nowtechnologies/open_PAPR/blower/firmware/attiny85/main.cpp

/*
 * papr_blower_attiny85.cpp
 *
 * Author : vmp
 */ 

#include <stdint.h>
#include <avr/io.h>
#include "../application/applicationInterface.h"

int main(void) {
  applicationSetup();
  applicationLoop();
  while (1) {
  }
}
