nowtechnologies/open_PAPR/blower/firmware/stm32g031j6/papr_blower_stm32g031j6_bsp.cpp

/// STM32G031J6 Board Support Package

#include "main.h"
#include "bspInterface.h"
#include "applicationInterface.h"

extern ADC_HandleTypeDef hadc1;
extern DMA_HandleTypeDef hdma_adc1;
extern TIM_HandleTypeDef htim17;

namespace {
  constexpr uint32_t cAdcChannelCount = ((uint32_t)  4);
  constexpr uint32_t cAdcSampleCount = ((uint32_t)  64);
  constexpr uint32_t cAdcBufferSize =   ((uint32_t)  cAdcSampleCount * cAdcChannelCount);
  constexpr uint32_t cIndexAdcBattery =  0u;
  constexpr uint32_t cIndexAdcPotmeter = 1u;
  constexpr uint32_t cIndexAdcTemp =     2u;
  constexpr uint32_t cIndexAdcVref =     3u;
  
  volatile uint16_t adcBuffer[cAdcBufferSize];
  volatile uint32_t adcData[cAdcChannelCount];
  
  ADC_HandleTypeDef &handleAdc = hadc1;
  DMA_HandleTypeDef &handleDmaAdc = hdma_adc1;
  TIM_HandleTypeDef &handleTimer = htim17;
  uint32_t timerChannel = TIM_CHANNEL_1;
  
  /// Calculating ADC oversample average
  void calculateAndCopyAdcData(uint32_t const start, uint32_t const end) {
    for (unsigned int i = start; i < end; i++) {
      adcData[i % cAdcChannelCount] += adcBuffer[i];
      adcData[i % cAdcChannelCount] /= 2;
    }
  }
  
}

/// HAL callback
extern "C" void HAL_ADC_ConvCpltCallback(ADC_HandleTypeDef* hadc) {
  calculateAndCopyAdcData(cAdcBufferSize / 2, cAdcBufferSize);
}

/// HAL callback
extern "C" void HAL_ADC_ConvHalfCpltCallback(ADC_HandleTypeDef* hadc) {
  calculateAndCopyAdcData(0, cAdcBufferSize / 2);
}

extern "C" void applicationSetup() {
  // Calibrate ADC
  if (HAL_ADCEx_Calibration_Start(&handleAdc) != HAL_OK) {
    Error_Handler();
  }
  // Start ADC DMA
  if (HAL_ADC_Start_DMA(&handleAdc, (uint32_t *)adcBuffer, cAdcBufferSize) != HAL_OK) {
    Error_Handler();
  }
  // PWM Timer setup
  __HAL_TIM_SET_PRESCALER(&handleTimer, 3); //0 = 5.8 kHz, 1 = 2 kHz, 3 = 1.5 kHz (48 MHz CPU & 0xFFF max)
  HAL_TIM_PWM_Start(&handleTimer, timerChannel);
}

// System
uint32_t papr::getTick() {
  return HAL_GetTick();
}

void papr::delayMs(uint32_t const aDelayMs) {
  HAL_Delay(aDelayMs);
}

// Power LED
void papr::turnOnPowerLed() {
  //HAL_GPIO_WritePin(POWER_LED_GPIO_Port, POWER_LED_Pin, GPIO_PIN_SET);
}

void papr::turnOffPowerLed() {
  //HAL_GPIO_WritePin(POWER_LED_GPIO_Port, POWER_LED_Pin, GPIO_PIN_RESET);
}

void papr::togglePowerLed() {
  //HAL_GPIO_TogglePin(POWER_LED_GPIO_Port, POWER_LED_Pin);
}

bool papr::isPowerLedOn() {
  //return HAL_GPIO_ReadPin(POWER_LED_GPIO_Port, POWER_LED_Pin) == GPIO_PIN_SET;
  return false;
}

// Mode LED
void papr::turnOnModeLed() {
  HAL_GPIO_WritePin(MODE_LED_GPIO_Port, MODE_LED_Pin, GPIO_PIN_SET);
}

void papr::turnOffModeLed() {
  HAL_GPIO_WritePin(MODE_LED_GPIO_Port, MODE_LED_Pin, GPIO_PIN_RESET);
}

void papr::toggleModeLed() {
  HAL_GPIO_TogglePin(MODE_LED_GPIO_Port, MODE_LED_Pin);
}

bool papr::isModeLedOn() {
  return HAL_GPIO_ReadPin(MODE_LED_GPIO_Port, MODE_LED_Pin) == GPIO_PIN_SET;
}

// Buzzer
void papr::turnOnBuzzer() {
  HAL_GPIO_WritePin(BUZZER_GPIO_Port, BUZZER_Pin, GPIO_PIN_SET);
}

void papr::turnOffBuzzer() {
  HAL_GPIO_WritePin(BUZZER_GPIO_Port, BUZZER_Pin, GPIO_PIN_RESET);
}

bool papr::isBuzzerOn() {
  return HAL_GPIO_ReadPin(BUZZER_GPIO_Port, BUZZER_Pin) == GPIO_PIN_SET;
  return false;
}

// ADC
uint32_t papr::getPotmeterValue() {
  return adcData[cIndexAdcPotmeter];
}

uint32_t papr::getBatteryValue() {
  return adcData[cIndexAdcBattery];
}

// Motor
void papr::setMotorPwm(uint32_t const aMotorPwm) {
  __HAL_TIM_SET_COMPARE(&handleTimer, timerChannel, aMotorPwm);
}
